Tejasva108/Concept-Design-And-Prototype-Development-Of-A-UGV-UAV-Transformer/Concept-Design-And-Prototype-Development-Of-A-UGV-UAV-Transformer/Solidworks files/Base_x4.STL

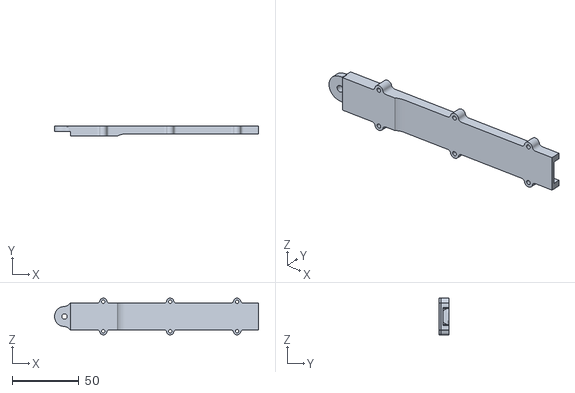
[picture p34: CAD file, 2025-10-22]
Concept-Design-And-Prototype-Development-Of-A-UGV-UAV-Transformer/Solidworks files/Base_x4.STL
152.5 x 7.50 x 27.5
