Tejasva108/Concept-Design-And-Prototype-Development-Of-A-UGV-UAV-Transformer/Concept-Design-And-Prototype-Development-Of-A-UGV-UAV-Transformer/STL files/Electronics_Tray_x1_new.STL

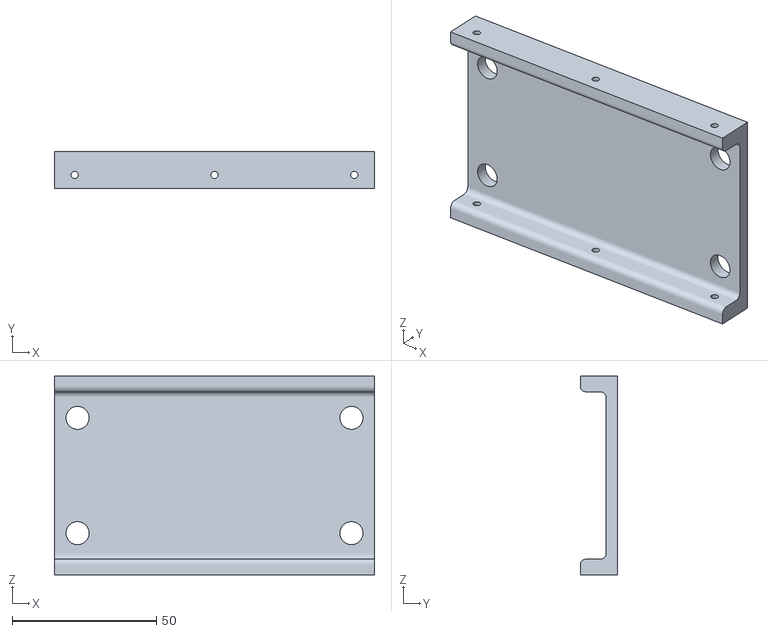
[picture p35: CAD file, 2025-10-22]
Concept-Design-And-Prototype-Development-Of-A-UGV-UAV-Transformer/STL files/Electronics_Tray_x1_new.STL
111.0 x 13.0 x 69.0
