Tejasva108/Concept-Design-And-Prototype-Development-Of-A-UGV-UAV-Transformer/Concept-Design-And-Prototype-Development-Of-A-UGV-UAV-Transformer/Solidworks files/BLDC_Motor_5010.SLDPRT

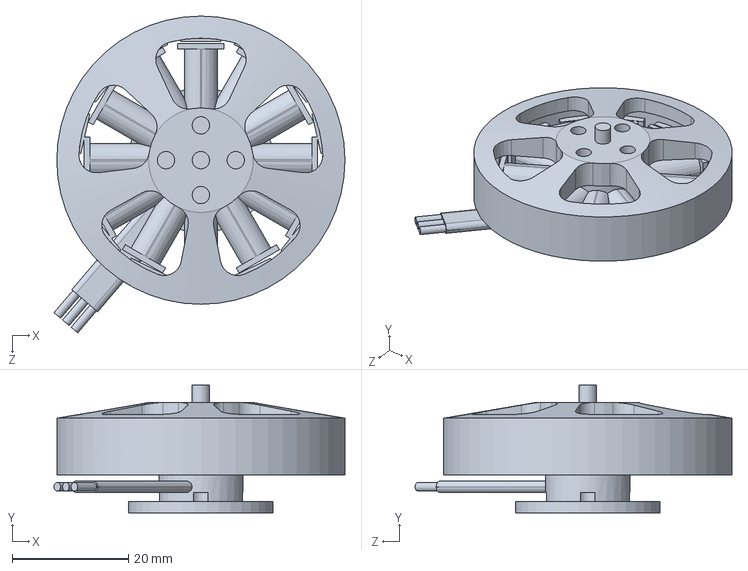
[picture p36: CAD file, 2025-10-22]
Concept-Design-And-Prototype-Development-Of-A-UGV-UAV-Transformer/Solidworks files/BLDC_Motor_5010.SLDPRT
50.1 x 22.0 x 54.5 mm
