Tejasva108/Concept-Design-And-Prototype-Development-Of-A-UGV-UAV-Transformer/Concept-Design-And-Prototype-Development-Of-A-UGV-UAV-Transformer/Solidworks files/Servo_Drive_Gear_modified.SLDPRT

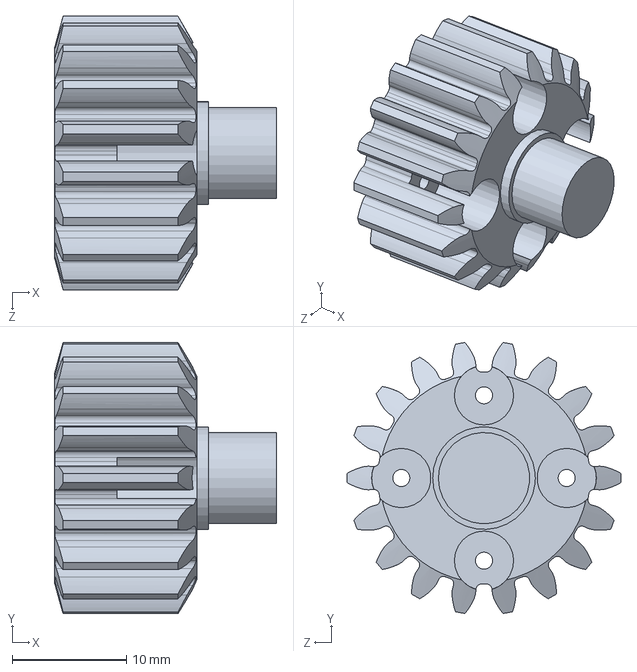
[picture p37: CAD file, 2025-10-22]
Concept-Design-And-Prototype-Development-Of-A-UGV-UAV-Transformer/Solidworks files/Servo_Drive_Gear_modified.SLDPRT
19.5 x 23.8 x 24.0 mm
