Tejasva108/Concept-Design-And-Prototype-Development-Of-A-UGV-UAV-Transformer/Concept-Design-And-Prototype-Development-Of-A-UGV-UAV-Transformer/STL files/Hub_Lock_x4.stl

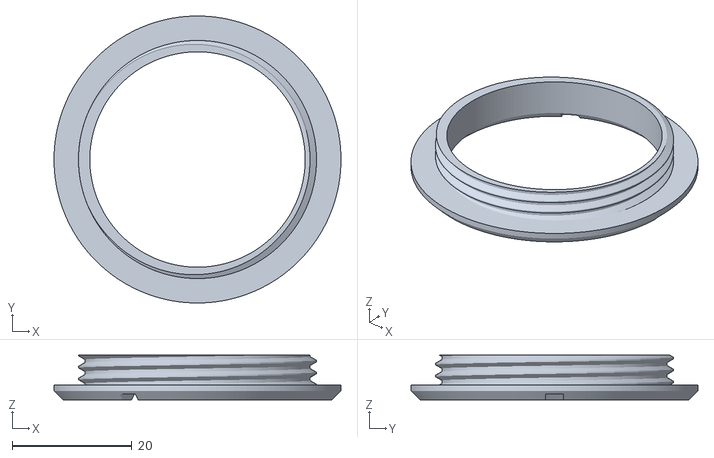
[picture p38: CAD file, 2025-10-22]
Concept-Design-And-Prototype-Development-Of-A-UGV-UAV-Transformer/STL files/Hub_Lock_x4.stl
48.0 x 48.0 x 7.50
