Tejasva108/Concept-Design-And-Prototype-Development-Of-A-UGV-UAV-Transformer/Concept-Design-And-Prototype-Development-Of-A-UGV-UAV-Transformer/STL files/Servo_Drive_Gear_100%_x2.stl

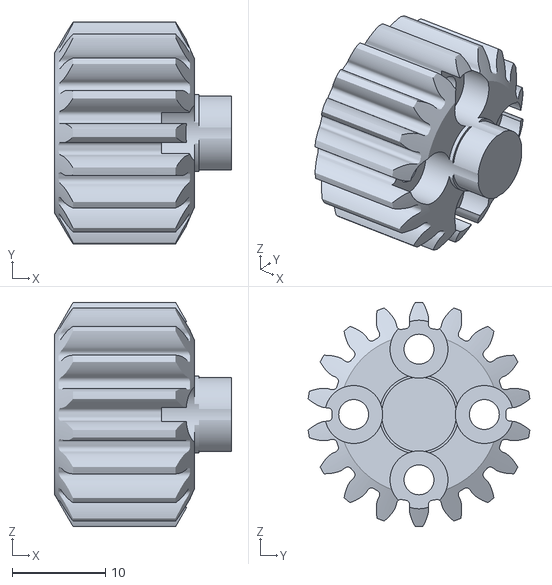
[picture p39: CAD file, 2025-10-22]
Concept-Design-And-Prototype-Development-Of-A-UGV-UAV-Transformer/STL files/Servo_Drive_Gear_100%_x2.stl
19.0 x 23.8 x 24.0
