Tejasva108/Concept-Design-And-Prototype-Development-Of-A-UGV-UAV-Transformer/Concept-Design-And-Prototype-Development-Of-A-UGV-UAV-Transformer/Solidworks files/Servo_Side_Gear.SLDPRT

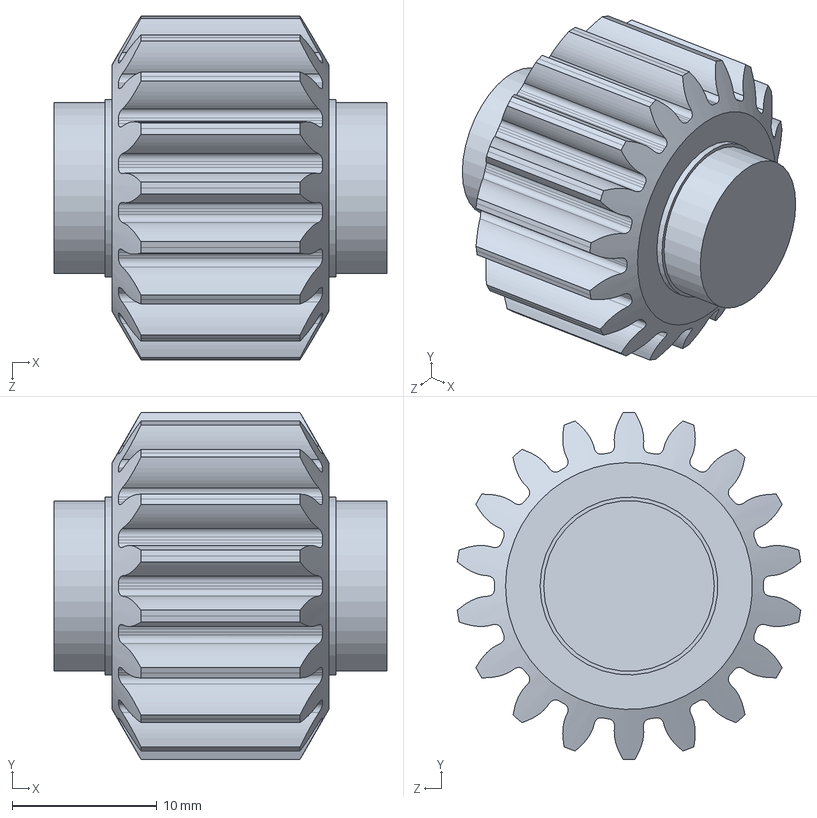
[picture p40: CAD file, 2025-10-22]
Concept-Design-And-Prototype-Development-Of-A-UGV-UAV-Transformer/Solidworks files/Servo_Side_Gear.SLDPRT
23.0 x 24.0 x 23.8 mm
