Tejasva108/Concept-Design-And-Prototype-Development-Of-A-UGV-UAV-Transformer/Concept-Design-And-Prototype-Development-Of-A-UGV-UAV-Transformer/STL files/Side_Plate_DXF_x2.dxf

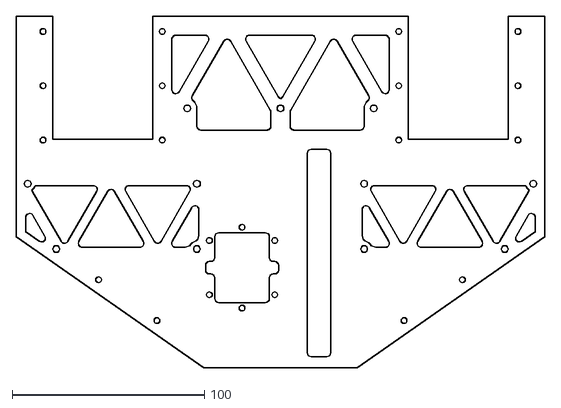
[picture p41: CAD file, 2025-10-22]
Concept-Design-And-Prototype-Development-Of-A-UGV-UAV-Transformer/STL files/Side_Plate_DXF_x2.dxf
275.0 x 183.0
