Tejasva108/Concept-Design-And-Prototype-Development-Of-A-UGV-UAV-Transformer/Concept-Design-And-Prototype-Development-Of-A-UGV-UAV-Transformer/Solidworks files/Part11.STEP

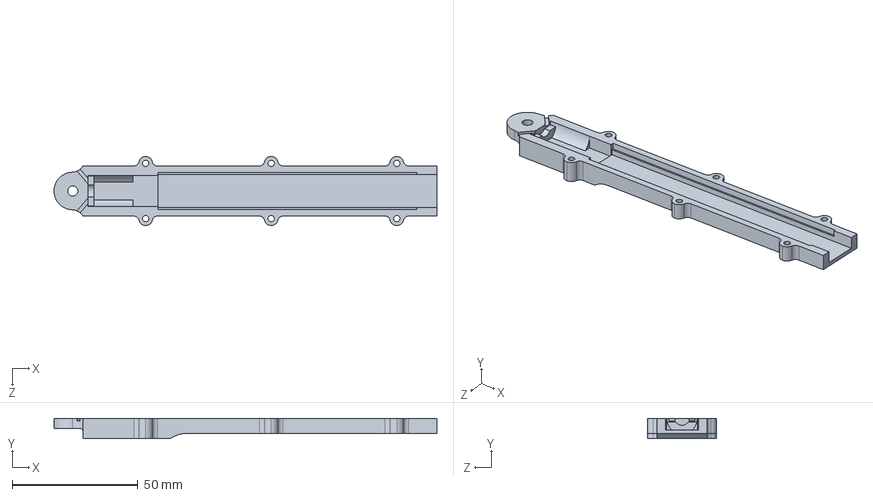
[picture p42: CAD file, 2025-10-21]
Concept-Design-And-Prototype-Development-Of-A-UGV-UAV-Transformer/Solidworks files/Part11.STEP
152.5 x 8.00 x 27.5 mm
