Tejasva108/Concept-Design-And-Prototype-Development-Of-A-UGV-UAV-Transformer/Concept-Design-And-Prototype-Development-Of-A-UGV-UAV-Transformer/STL files/Roller_Bearing_20%_x4.stl

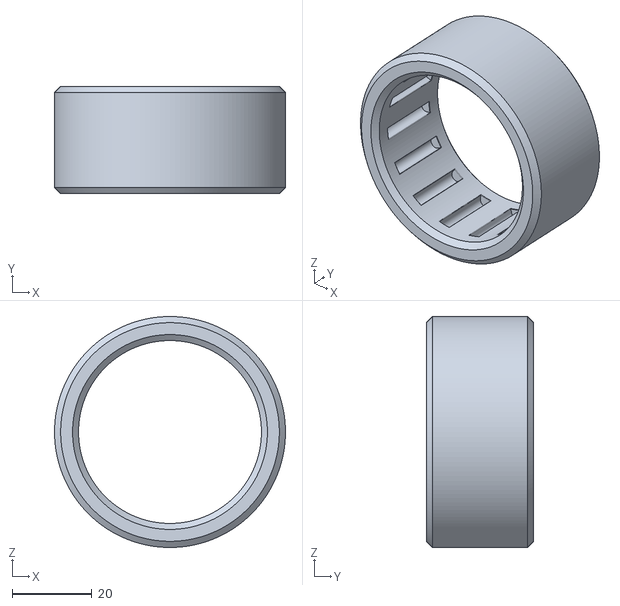
[picture p43: CAD file, 2025-10-22]
Concept-Design-And-Prototype-Development-Of-A-UGV-UAV-Transformer/STL files/Roller_Bearing_20%_x4.stl
58.1 x 27.0 x 58.1
