Tejasva108/Concept-Design-And-Prototype-Development-Of-A-UGV-UAV-Transformer/Concept-Design-And-Prototype-Development-Of-A-UGV-UAV-Transformer/Solidworks files/PROPELLER - 8x4.5 CCW.step.SLDPRT

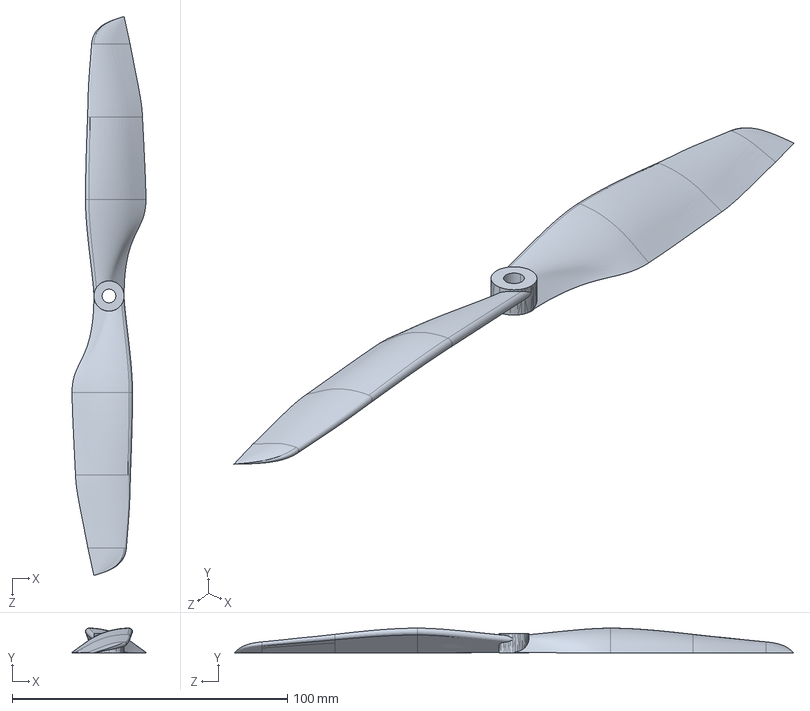
[picture p44: CAD file, 2025-10-21]
Concept-Design-And-Prototype-Development-Of-A-UGV-UAV-Transformer/Solidworks files/PROPELLER - 8x4.5 CCW.step.SLDPRT
26.9 x 9.01 x 203.2 mm
