Tejasva108/Concept-Design-And-Prototype-Development-Of-A-UGV-UAV-Transformer/Concept-Design-And-Prototype-Development-Of-A-UGV-UAV-Transformer/Solidworks files/Part1 Cover.SLDPRT

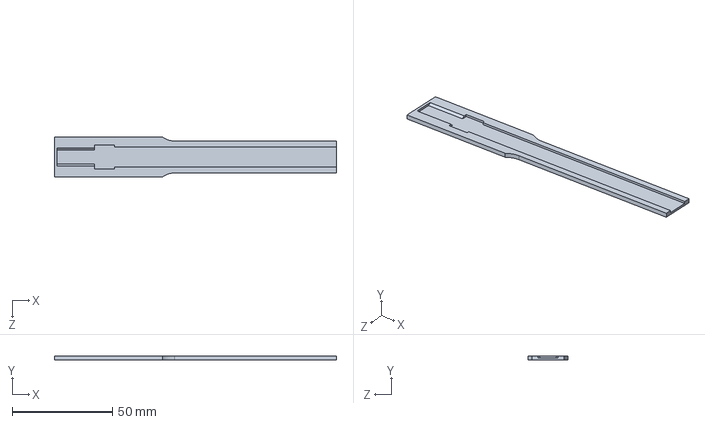
[picture p45: CAD file, 2025-10-21]
Concept-Design-And-Prototype-Development-Of-A-UGV-UAV-Transformer/Solidworks files/Part1 Cover.SLDPRT
141.0 x 2.00 x 20.0 mm
