Tejasva108/Concept-Design-And-Prototype-Development-Of-A-UGV-UAV-Transformer/Concept-Design-And-Prototype-Development-Of-A-UGV-UAV-Transformer/Solidworks files/Part2.SLDPRT

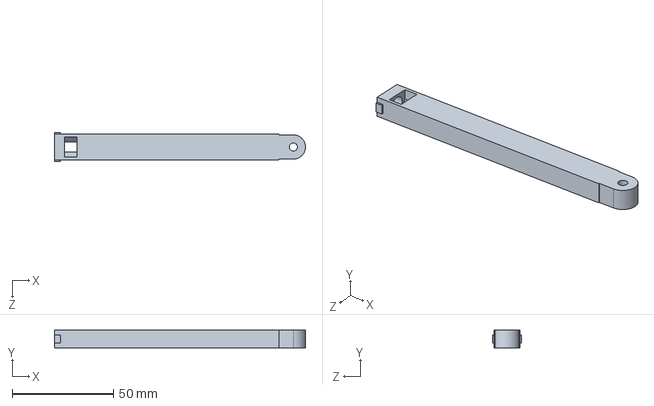
[picture p46: CAD file, 2025-10-21]
Concept-Design-And-Prototype-Development-Of-A-UGV-UAV-Transformer/Solidworks files/Part2.SLDPRT
124.0 x 8.70 x 14.2 mm
