Tejasva108/Concept-Design-And-Prototype-Development-Of-A-UGV-UAV-Transformer/Concept-Design-And-Prototype-Development-Of-A-UGV-UAV-Transformer/Solidworks files/rod.SLDPRT

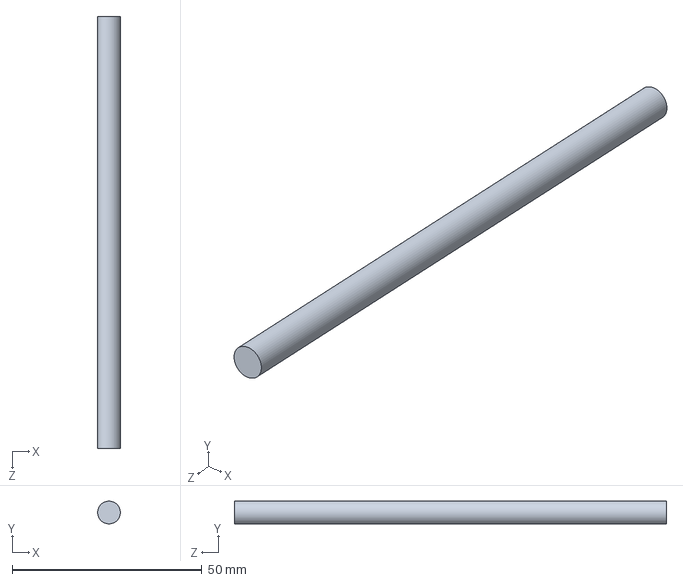
[picture p47: CAD file, 2025-10-21]
Concept-Design-And-Prototype-Development-Of-A-UGV-UAV-Transformer/Solidworks files/rod.SLDPRT
6.00 x 6.00 x 113.7 mm
