Tejasva108/Concept-Design-And-Prototype-Development-Of-A-UGV-UAV-Transformer/Concept-Design-And-Prototype-Development-Of-A-UGV-UAV-Transformer/Solidworks files/Lift_Arm_Right_x2.SLDPRT

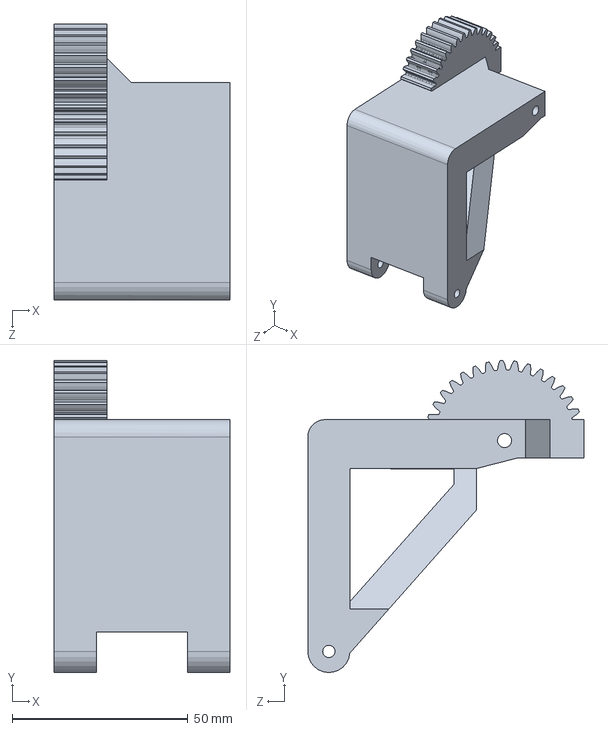
[picture p48: CAD file, 2025-10-21]
Concept-Design-And-Prototype-Development-Of-A-UGV-UAV-Transformer/Solidworks files/Lift_Arm_Right_x2.SLDPRT
50.0 x 88.8 x 78.7 mm
